Albert-IV/om-keyboard/rev3/pcb/footprints/kleeb/models/MBK-1u.step

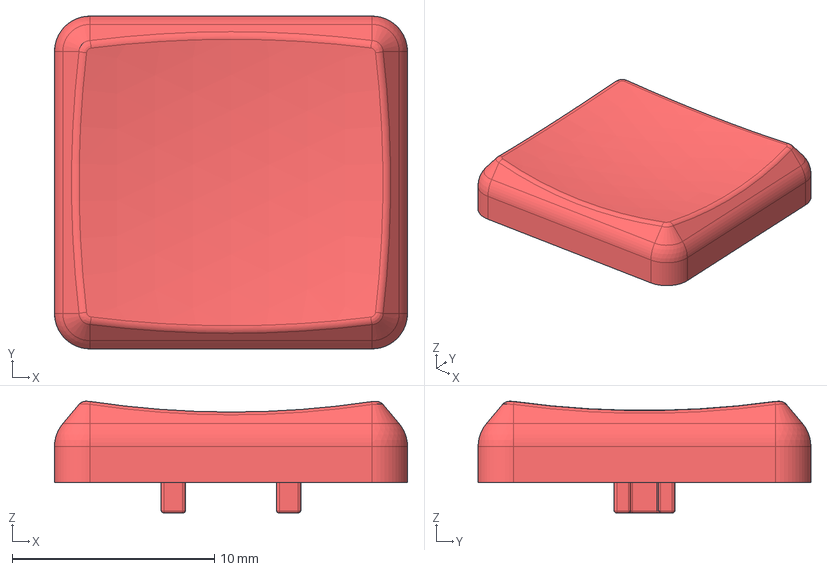
[picture p19: CAD file, 2022-11-13]
rev3/pcb/footprints/kleeb/models/MBK-1u.step
17.4 x 16.4 x 5.52 mm
