Albert-IV/om-keyboard/rev3/pcb/footprints/kleeb/models/hro-type-c-31-m-12.step

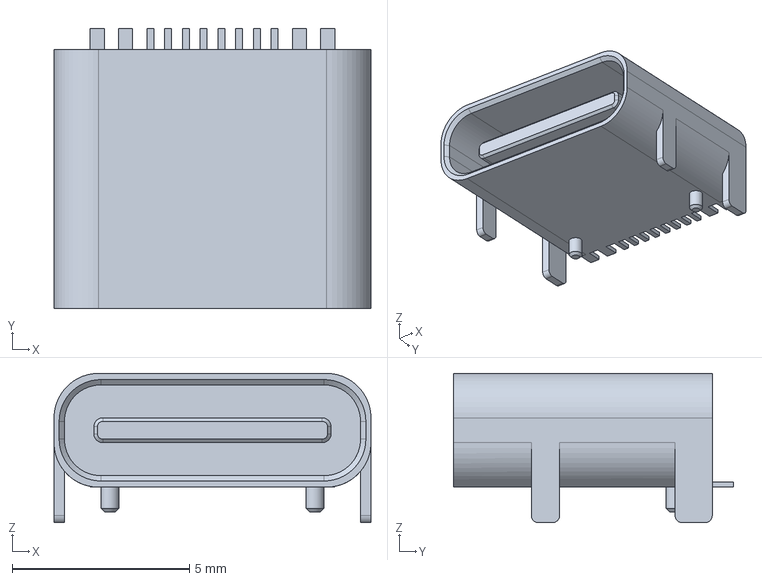
[picture p20: CAD file, 2022-11-13]
rev3/pcb/footprints/kleeb/models/hro-type-c-31-m-12.step
8.94 x 7.90 x 4.21 mm
