Albert-IV/om-keyboard/rev3/pcb/footprints/kleeb/models/pg1350.step

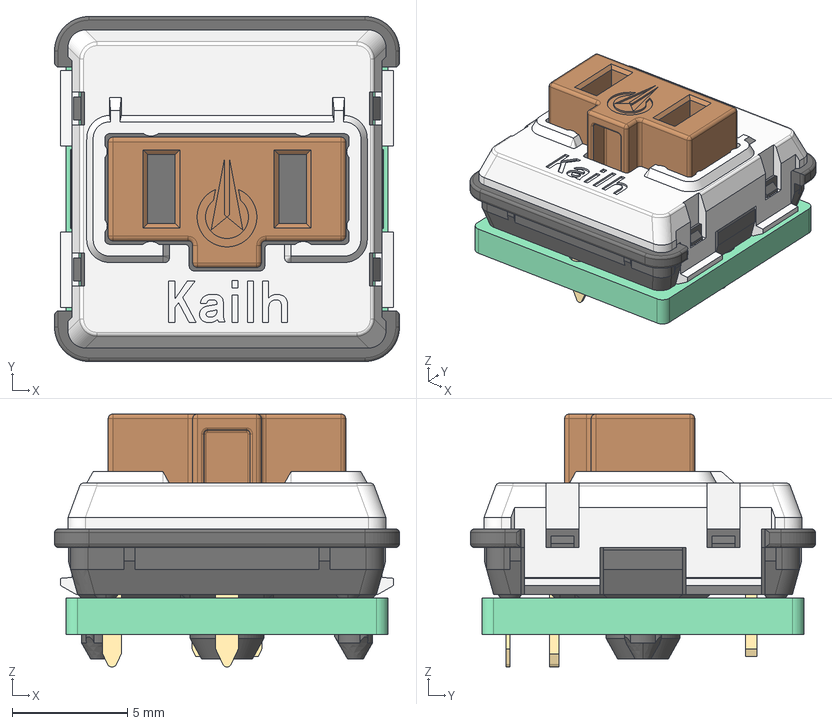
[picture p21: CAD file, 2022-11-13]
rev3/pcb/footprints/kleeb/models/pg1350.step
15.0 x 15.0 x 11.0 mm
