Albert-IV/om-keyboard/rev2/full-case/bottom.dxf

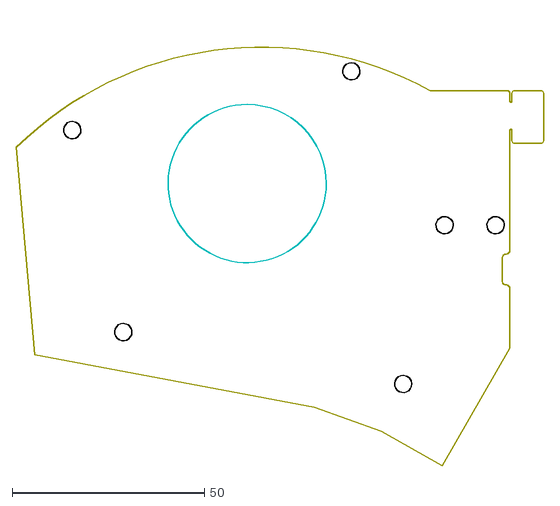
[picture p22: CAD file, 2022-11-13, an earlier design]
rev2/full-case/bottom.dxf
137.0 x 116.9
